aKaReZa75/RCS_AVR/Firmware/src/main.c

#include "aKaReZa.h"



int main(void)
{
  outputs_Init();
  display_Init();
  display_Update();
  millis_Init();
  usart_Init(Initialize);
  globalInt_Enable;

  while(1)
  {
    scheduler();
  };
};
